TiNredmc/IOLinky/Software/IOLinky_v1.0/src/src_iol/iol_dl.h

#ifndef IOL_DL_H
#define IOL_DL_H

#include <stdint.h>
#include <string.h>

#include "iol_pl.h"

// DL Main FSM enums
enum DL_MAIN_FSM{
	DL_MFSM_PR	= 0,// Wait for message read
	DL_MFSM_WFWR		// Write reply and wait for done
};

enum DL_MODE_FSM{
	DL_MODE_STARTUP = 0,
	DL_MODE_PREOP,
	DL_MODE_OP
};

enum DL_MTYPE{
	MSEQ_MTYPE_0 = 0,
	MSEQ_MTYPE_1 = 1,
	MSEQ_MTYPE_2 = 2
};

typedef struct __attribute__((packed)){
	union{
		uint8_t MC;
		struct{
			uint8_t ADDR	:5;// Address
			uint8_t CC		:2;// Commu Channel
			uint8_t RW		:1;// Read/Write
		}MCBit;
	};
	
	union{
		uint8_t CKT;
		struct{
			uint8_t CKT		:6;// Checksum
			uint8_t MT		:2;// M-sequence type
		}CKTBit;
	};
	
	uint8_t OD;// On-request Data
	
	union{
		uint8_t CKS;
		struct{
			uint8_t CKS		:6;// Checksum
			uint8_t PD		:1;// PD status
			uint8_t EV		:1;// Event flag
		}CKSBit;
	};
}iol_mtype_0_t;

typedef struct __attribute__((packed)){
	union{
		uint8_t MC;
		struct{
			uint8_t ADDR	:5;// Address
			uint8_t CC		:2;// Commu Channel
			uint8_t RW		:1;// Read/Write
		}MCBit;
	};
	
	union{
		uint8_t CKT;
		struct{
			uint8_t CKT		:6;// Checksum
			uint8_t MT		:2;// M-sequence type
		}CKTBit;
	};
	
	uint8_t OD[2];// On-request Data
	
	union{
		uint8_t CKS;
		struct{
			uint8_t CKS		:6;// Checksum
			uint8_t PD		:1;// PD status
			uint8_t EV		:1;// Event flag
		}CKSBit;
	};
	
}iol_mtype_1_2_t;

typedef struct __attribute__((packed)){
	union{
		uint8_t MC;
		struct{
			uint8_t ADDR	:5;// Address
			uint8_t CC		:2;// Commu Channel
			uint8_t RW		:1;// Read/Write
		}MCBit;
	};
	
	union{
		uint8_t CKT;
		struct{
			uint8_t CKT		:6;// Checksum
			uint8_t MT		:2;// M-sequence type
		}CKTBit;
	};
	
	uint8_t OD;// On-request Data
	
	// Process Data
	uint8_t  PD[2];

	union{
		uint8_t CKS;
		struct{
			uint8_t CKS		:6;// Checksum
			uint8_t PD		:1;// PD status
			uint8_t EV		:1;// Event flag
		}CKSBit;
	};
	
}iol_mtype_2_2_t;


typedef struct __attribute__((packed)){
	union{
		uint8_t MC;
		struct{
			uint8_t ADDR	:5;// Address
			uint8_t CC		:2;// Commu Channel
			uint8_t RW		:1;// Read/Write
		}MCBit;
	};
	
	union{
		uint8_t CKT;
		struct{
			uint8_t CKT		:6;// Checksum
			uint8_t MT		:2;// M-sequence type
		}CKTBit;
	};
	
	uint8_t OD;// On-request Data
	
	// Process Data
	union{
		uint8_t  PD[8];
		struct{
			uint16_t psu_stat;
			uint16_t iout;
			uint16_t vout;
			uint16_t vin;
		}PDWord;
	};
	
	union{
		uint8_t CKS;
		struct{
			uint8_t CKS		:6;// Checksum
			uint8_t PD		:1;// PD status
			uint8_t EV		:1;// Event flag
		}CKSBit;
	};
	
}iol_mtype_2_V_8PDI_t;

typedef struct{
	union{
		uint8_t Iservice;
		struct{
			uint8_t length:4;
			uint8_t Iserv	:4;
		};		
	};
	
	uint8_t ExtLength;
	uint8_t Index[2];
	uint8_t Subindex;

}iol_isdu_t;

typedef struct __attribute__((packed)){
	char *vendor_name;
	char *vendor_text;
	char *product_name;
	char *product_id;
	char *product_text;
	char *serial_number;
	char *hardware_revision;
	char *firmware_revision;
}isdu_data_t;

typedef struct{
	uint16_t (*isdu_handleRead)(
		uint16_t idx,
		uint8_t *out_buf_ptr
	);
	
	uint16_t (*isdu_handleWrite)(
		uint16_t idx,
		uint8_t *in_buf_ptr,
		uint16_t write_count,
		uint16_t data_offset
	);
	
}isdu_handler_t;

typedef struct __attribute__((packed)){
	
	union{
		uint8_t StatusCode;
		struct{
			uint8_t ActedEvt1		:1;
			uint8_t ActedEvt2		:1;
			uint8_t ActedEvt3		:1;
			uint8_t ActedEvt4		:1;
			uint8_t ActedEvt5		:1;
			uint8_t ActedEvt6		:1;
			uint8_t res1				:1;
			uint8_t EvtDetails	:1;// Always 1
		}StatusCodeBit;
	};
	
	struct __attribute__((packed)){
		union{
			uint8_t EventQualifier;
			struct{
				uint8_t instant		:3;
				uint8_t	source		:1;
				uint8_t type			:2;
				uint8_t mode			:2;
			}EventQualifierBit;
		};
		uint16_t EventCode;
	}EventSlot[6];
	
}iol_event_t;

// Extern for msg handler 
extern uint8_t dl_main_fsm;
extern uint32_t timeout_counter;

extern uint8_t PD_setFlag;
extern uint8_t master_cmd;
extern uint8_t master_cycle;

extern uint8_t *direct_param_ptr;

// Extern for ISDU
extern isdu_handler_t *isdu_pHandler_t;
extern iol_isdu_t 		iol_iservice;

extern uint8_t dl_isdu_fsm;
extern uint8_t ISDU_data_pointer;
extern uint8_t ISDU_data_offset_index;
extern uint8_t ISDU_data_count;
extern uint8_t ISDU_in_buffer[70];
extern uint8_t ISDU_out_buffer[70];
extern uint8_t ISDU_RWflag;
extern uint8_t ISDU_16bIndex;

extern isdu_data_t *isdu_device_data_t;
extern uint8_t *pdIn_ptr;

// Extern for Diagnosis event page
extern iol_event_t	iol_evt_t;

void iol_dl_init(
	uint8_t *dev_param_1_ptr,
	isdu_handler_t *isdu_ptrHandler_t,
	isdu_data_t *isdu_data_ptr_t,
	uint8_t *pd_in_ptr,
	uint8_t pd_in_cnt
	);

void iol_dl_poll();
uint8_t iol_dl_getModeStatus();
void iol_dl_updatePD();

void iol_dl_pushEvt(
	uint8_t eventType,
	uint16_t eventCode
	);

void iol_dl_popEvt();

#endif
