TiNredmc/IOLinky/Software/IOLinky-F042/src/src_drv/usart.h

#ifndef USART_H
#define USART_H

#include <stdint.h>
#include "stm32f042x6.h"
#include "gpio_pinout.h"

enum IOL_COM_MODE{
	COM1 = 0,
	COM2,
	COM3,
};

void usart_initIOLink(
	uint8_t com_mode,				// IO-Link COM speed
	uint8_t read_size_max,	// RX buffer size
	uint8_t *read_ptr,				// RX buffer
	uint8_t *write_ptr				// TX buffer
	);

void usart_writeRequest(
	uint8_t count);
uint8_t usart_pollWrite();

uint8_t usart_getReadIdx();
void usart_resetReadIdx();

uint8_t usart_getPEStatus();

void usart_dmaWriteStart(
	uint8_t *data_ptr, 
	uint8_t data_len
	);

#endif
