TiNredmc/IOLinky/Software/EVLIOL4LSV1/src/src_drv/spi.h

#ifndef SPI_H
#define SPI_H

#include <stdint.h>
#include <stdio.h>

#include "stm32g071xx.h"
#include "gpio_pinout.h"
#include "Systick_delay.h"

void spi_init();

void spi_read(uint8_t *data, size_t len);
void spi_Write(uint8_t *data, size_t len);

void spi_WriteAndRead(
	uint8_t *TXbuf, 
	uint8_t *RXbuf,
	size_t len);

void spi_WriteOnceAndRead(
	uint8_t TX,
	uint8_t *RXbuf,
	size_t len);

void spi_WriteOnceAndWrite(
	uint8_t TX,
	uint8_t *TXbuf,
	size_t len);

uint8_t spi_l6364FastReadFF(
	uint8_t *FR,
	uint8_t *statusReg,
  uint32_t timeout
	);

uint8_t spi_l6364FastWriteFF(
		uint8_t count,
		uint8_t *FR,
		uint8_t *statusReg,
    uint32_t timeout
	);

#endif
